Rdisrael/Projeto-Bluepill/ShieldBluepill V2/Simbolo, pegada e modelo 3D/Modelos 3D/micro-switch-7x7.step

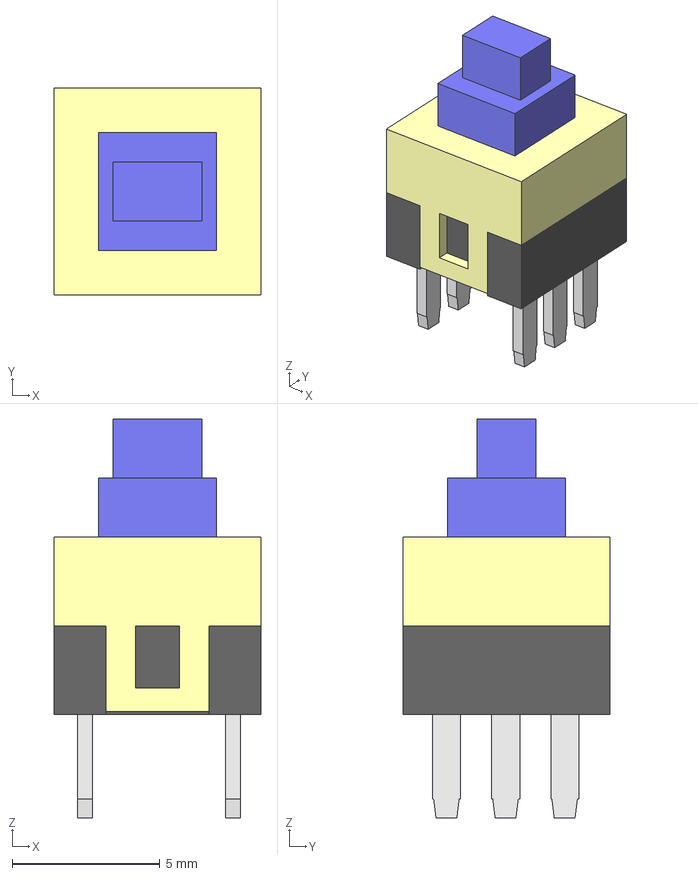
[picture p18: CAD file, 2024-04-01]
ShieldBluepill V2/Simbolo, pegada e modelo 3D/Modelos 3D/micro-switch-7x7.step
7.00 x 7.00 x 13.5 mm
Górny-zatrzaski
Otwór-dolny
Przycisk-dol
Pins-1-2-3
Przycisk-g鏎a
Pins-4-5-6
