Rdisrael/Projeto-Bluepill/ShieldBluepill V2/Simbolo, pegada e modelo 3D/Modelos 3D/ESP-01S_RevA.STEP

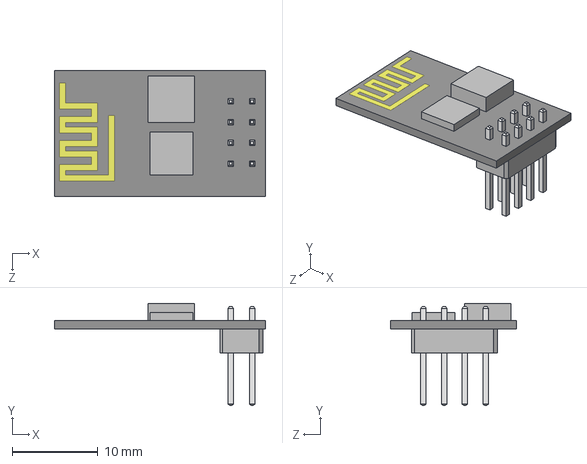
[picture p19: CAD file, 2024-04-01]
ShieldBluepill V2/Simbolo, pegada e modelo 3D/Modelos 3D/ESP-01S_RevA.STEP
24.6 x 11.9 x 14.7 mm
